foxgloveinstruments/fluxharmonium/src/tiny2040/config.py

from note_map import *

DEBUG = False

NUMBER_OF_NOTES = len(NOTE_MAP)
NUMBER_OF_DACS = 12

CONTROL_RATE = 200
CONTROL_RATE_SEC = 0.005 #0.0025 # 1/CONTROL_RATE

# ATTACK_MULT = 0.5

# MIDI Constants (OFFSET BY -1)
MIDI_LOW_VALUE = 24
MIDI_HIGH_VALUE = 119
CTRL_SEC_DIV = 12.7 # gives a range of 10 sec for MIDI range 0-127

DAC_STARTUP_VALUE = 128

OUT_VOL_CHAN = 0

ENV_MODE_CHAN = 0
ENV_MODE_CTRL = 0

ENV_ATTACK_CHAN = 1
ENV_RELEASE_CHAN = 2

HARM_MODE_CHAN = 0
HARM_MODE_CTRL = 6
HARM_SUB8_CTRL = 7
HARM_SUB3_CTRL = 8
HARM_UNIS_CTRL = 9
HARM_OCT_CTRL = 10
HARM_3RD_CTRL = 11
HARM_4TH_CTRL = 12
HARM_5TH_CTRL = 13
HARM_6TH_CTRL = 14
HARM_8TH_CTRL = 15
HARM_9TH_CTRL = 16
HARM_12TH_CTRL = 17
HARM_15TH_CTRL = 18
HARM_17TH_CTRL = 19
HARM_18TH_CTRL = 20
HARM_19TH_CTRL = 21

# not currently used
# with testing sound was lost at about 128 so this range was too high
MIDI_DAC_MAP = [
    169,168,167,166,164,163,162,160,
    159,158,156,155,154,152,151,150,
    148,147,146,144,143,142,140,139,
    138,136,135,134,132,131,130,128,
    127,126,124,123,122,120,119,118,
    116,115,114,112,111,110,108,107,
    106,104,103,102,100,99,98,96,
    95,94,92,91,90,88,87,86,
    84,83,82,80,79,78,76,75,
    74,72,71,70,68,67,66,64,
    63,62,60,59,58,56,55,54,
    52,51,50,48,47,46,44,43,
    42,40,39,38,36,35,34,32,
    31,30,28,27,26,24,23,22,
    20,19,18,16,15,14,12,11,
    10,8,7,6,4,3,2,0,
]
