foxgloveinstruments/fluxharmonium/src/tiny2040/note_map.py

""" 
Map of incoming MIDI note to DAC output number. 
midi note: {
    map [1-96], # the output is translated to keep all notes in octave order 
    output number [1-96],
    dac [1-12],
    address [1-8],
"""
NOTE_MAP = {
    24: {'map': 89, 'output': 96, 'card': 6, 'dac': 12, 'address': 1},
    25: {'map': 33, 'output': 40, 'card': 3, 'dac': 5, 'address': 1},
    26: {'map': 73, 'output': 80, 'card': 5, 'dac': 10, 'address': 1},
    27: {'map': 17, 'output': 24, 'card': 2, 'dac': 3, 'address': 1},
    28: {'map': 57, 'output': 64, 'card': 4, 'dac': 8, 'address': 1},
    29: {'map': 1, 'output': 8, 'card': 1, 'dac': 1, 'address': 1},
    30: {'map': 41, 'output': 48, 'card': 3, 'dac': 6, 'address': 1},
    31: {'map': 81, 'output': 88, 'card': 6, 'dac': 11, 'address': 1},
    32: {'map': 25, 'output': 32, 'card': 2, 'dac': 4, 'address': 1},
    33: {'map': 65, 'output': 72, 'card': 5, 'dac': 9, 'address': 1},
    34: {'map': 9, 'output': 16, 'card': 1, 'dac': 2, 'address': 1},
    35: {'map': 49, 'output': 56, 'card': 4, 'dac': 7, 'address': 1},
    36: {'map': 90, 'output': 93, 'card': 6, 'dac': 12, 'address': 2},
    37: {'map': 34, 'output': 37, 'card': 3, 'dac': 5, 'address': 2},
    38: {'map': 74, 'output': 77, 'card': 5, 'dac': 10, 'address': 2},
    39: {'map': 18, 'output': 21, 'card': 2, 'dac': 3, 'address': 2},
    40: {'map': 58, 'output': 61, 'card': 4, 'dac': 8, 'address': 2},
    41: {'map': 2, 'output': 5, 'card': 1, 'dac': 1, 'address': 2},
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
    101: {'map': 7, 'output': 3, 'card': 1, 'dac': 1, 'address': 7},
    102: {'map': 47, 'output': 43, 'card': 3, 'dac': 6, 'address': 7},
    103: {'map': 87, 'output': 83, 'card': 6, 'dac': 11, 'address': 7},
    104: {'map': 31, 'output': 27, 'card': 2, 'dac': 4, 'address': 7},
    105: {'map': 71, 'output': 67, 'card': 5, 'dac': 9, 'address': 7},
    106: {'map': 15, 'output': 11, 'card': 1, 'dac': 2, 'address': 7},
    107: {'map': 55, 'output': 51, 'card': 4, 'dac': 7, 'address': 7},
    108: {'map': 96, 'output': 90, 'card': 6, 'dac': 12, 'address': 8},
    109: {'map': 40, 'output': 34, 'card': 3, 'dac': 5, 'address': 8},
    110: {'map': 80, 'output': 74, 'card': 5, 'dac': 10, 'address': 8},
    111: {'map': 24, 'output': 18, 'card': 2, 'dac': 3, 'address': 8},
    112: {'map': 64, 'output': 58, 'card': 4, 'dac': 8, 'address': 8},
    113: {'map': 8, 'output': 2, 'card': 1, 'dac': 1, 'address': 8},
    114: {'map': 48, 'output': 42, 'card': 3, 'dac': 6, 'address': 8},
    115: {'map': 88, 'output': 82, 'card': 6, 'dac': 11, 'address': 8},
    116: {'map': 32, 'output': 26, 'card': 2, 'dac': 4, 'address': 8},
    117: {'map': 72, 'output': 66, 'card': 5, 'dac': 9, 'address': 8},
    118: {'map': 16, 'output': 10, 'card': 1, 'dac': 2, 'address': 8},
    119: {'map': 56, 'output': 50, 'card': 4, 'dac': 7, 'address': 8},
}
