foxgloveinstruments/fluxharmonium/src/teensy/arduino/src/noteMap.h

/**
 * @brief 
 * Map of incoming MIDI note to DAC output number. 
 * midi note, output number
 */

#ifndef NOTEMAP_H
#define NOTEMAP_H

#include <map>

const std::map<int, int> NOTE_MAP = {
    {24, 89},
    {25, 33},
    {26, 73},
    {27, 17},
    {28, 57},
    {29, 1},
    {30, 41},
	{31, 81},
	{32, 25},
	{33, 65},
	{34, 9},
	{35, 49},
	{36, 90},
	{37, 34},
	{38, 74},
	{39, 18},
	{40, 58},
	{41, 2},
	{42, 42},
	{43, 82},
	{44, 26},
	{45, 66},
	{46, 10},
	{47, 50},
	{48, 91},
	{49, 35},
	{50, 75},
	{51, 19},
	{52, 59},
	{53, 3},
	{54, 43},
	{55, 83},
	{56, 27},
	{57, 67},
	{58, 11},
	{59, 51},
	{60, 92},
	{61, 36},
	{62, 76},
	{63, 20},
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
};

#endif
