foxgloveinstruments/fluxharmonium/src/tiny2040/envelopes.py

import asyncio

class Envelopes():
    def __init__(self, frequency, envelope_values, debug=False):
        self.envelopes = []
        self.frequency = frequency
        self.envelope_values = envelope_values
        self.debug = debug

    def add_envelope(self, envelope):
        self.envelopes.append(envelope)
        # self.envelope_values.append(0)

    async def run(self):
        while True:
            for envelope in enumerate(self.envelopes):
                env_val = next(envelope[1])
                if self.debug:
                    print(f'updating envelope {envelope[0]} {env_val}')
                self.envelope_values[envelope[0]] = env_val
            await asyncio.sleep(self.frequency)
