foxgloveinstruments/fluxharmonium/src/fluxharmonium/note_mapONE2ONE.py

# midi note: output number
# A 1:1 MAP of note to frequency position
# I may have been "double mapping"
NOTE_MAP = {
    24: 1,
    25: 2,
    26: 3,
    27: 4,
    28: 5,
    29: 6,
    30: 7,
    31: 8,
    32: 9,
    33: 10,
    34: 11,
    35: 12,
    36: 13,
    37: 14,
    38: 15,
    39: 16,
    40: 17,
    41: 18,
    42: 19,
    43: 20,
    44: 21,
    45: 22,
    46: 23,
    47: 24,
    48: 25,
    49: 26,
    50: 27,
    51: 28,
    52: 29,
    53: 30,
    54: 31,
    55: 32,
    56: 33,
    57: 34,
    58: 35,
    59: 36,
    60: 37,
    61: 38,
    62: 39,
    63: 40,
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
}
